Willist1/Projekt-Grupowy-Minutnik/AS7/MinutnixPol/lightsensor.h

/*
 * lightsensor.h
 *
 * Created: 4/27/2019 8:48:38 PM
 *  Author: stefa
 */ 


#ifndef LIGHTSENSOR_H_
#define LIGHTSENSOR_H_

#include <stdint.h>

#define DEFAULT_BRIGHTNESS 20 // %

void lightsensorInit();
uint8_t lightsensorRead();
void lightsensorSuspend();
void lightsensorResume();
uint8_t lightsensorFilter( uint8_t input );

#endif /* LIGHTSENSOR_H_ */
