Willist1/Projekt-Grupowy-Minutnik/AS7/MinutnixPol/encoder.h

/*
 * encoder.h
 *
 * Created: 3/13/2019 9:03:34 PM
 *  Author: stefa
 */ 


#ifndef ENCODER_H_
#define ENCODER_H_

int8_t Read1StepEncoder();
int8_t Read2StepEncoder();
int8_t Read4StepEncoder();

#endif /* ENCODER_H_ */
