Willist1/Projekt-Grupowy-Minutnik/AS7/MinutnixPol/pwrFail.h

/*
 * pwrFail.h
 *
 * Created: 3/14/2019 11:11:59 PM
 *  Author: stefan
 */ 


#ifndef PWRFAIL_H_
#define PWRFAIL_H_

void pwrFailInit();
void NVDataInit();

void EEPROMupdate();

#endif /* PWRFAIL_H_ */
