Willist1/Projekt-Grupowy-Minutnik/AS7/MinutnixPol/i2c.h

/*
 * i2c.h
 *
 * Created: 3/10/2019 1:21:25 PM
 *  Author: stefan
 */ 

#ifndef I2C_H_
#define I2C_H_

#include <stdint.h>
#include <util/twi.h>

#define I2CBUSCLOCK		50000UL

#define I2C_OK          0
#define I2C_STARTError	1
#define I2C_NoNACK		3
#define I2C_NoACK		4

extern uint8_t I2C_Error;
inline void I2C_SetError(uint8_t err) { I2C_Error=err;};

void I2C_Init();
void I2C_Start();
static inline void I2C_Stop() {TWCR = _BV(TWINT) | _BV(TWEN) | _BV(TWSTO);};	// Nadaj sygnal STOP
void I2C_SetBusSpeed(uint16_t speed);	// Ustaw predkosc magistrali I2C (Predkosc wyniesie speed*100[Hz])
void I2C_SendAddr(uint8_t address);		// Wyslij adres urzadzenia slave
void I2C_SendByte(uint8_t byte);		// Wyslij bajt danych do slave
uint8_t I2C_ReceiveData_ACK();			// Odbierz bajt danych od slave, wysylajac ACK
uint8_t I2C_ReceiveData_NACK();			// Odbierz bajt danych od slave, nie wysyaaj ACK
static inline void I2C_WaitForComplete() {while (!(TWCR & _BV(TWINT)));};	// Zaczekaj na koniec biezacej operacji I2C
static inline void I2C_WaitTillStopWasSent() {while (TWCR & _BV(TWSTO));};	// Zaczekaj na koniec nadawania sygnalu STOP
void I2C_SendStartAndSelect(uint8_t addr);									// Wyslij START i adres urzadzenia slave
void I2C_StartSelectWait(uint8_t addr);										// Wyslij START i adres urzadzenia slave - oczekuj na ACK

#endif /* I2C_H_ */
